DFonMor/Goniometro-Digital/Modelos 3D/goniometro.SLDASM

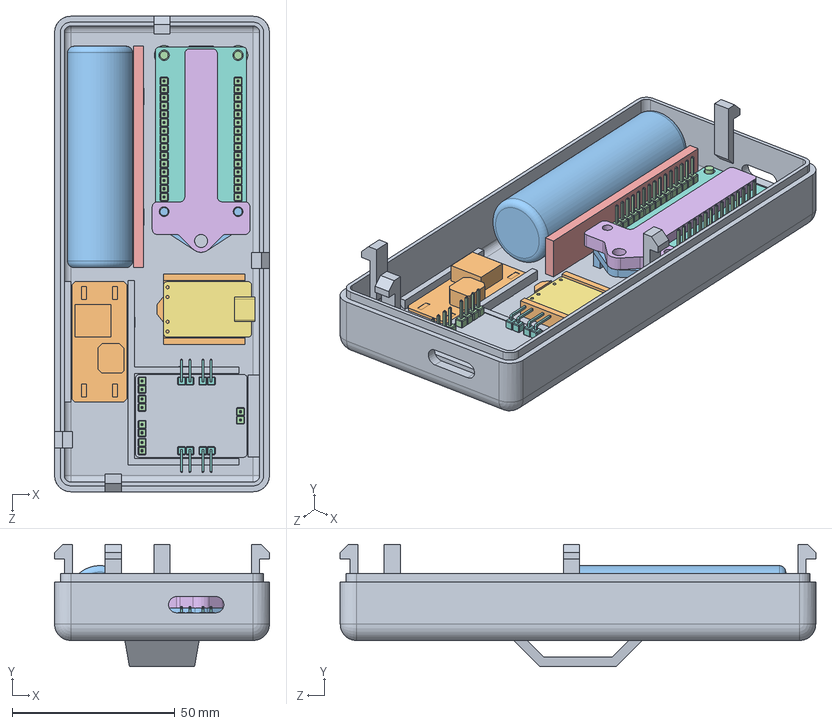
[picture p6: CAD file, 2026-04-27]
Modelos 3D/goniometro.SLDASM
66.0 x 37.5 x 146.0 mm
case_inferior
ESP32_board
esp32_connector x 2
ESP32_processor_base
ESP32_processor
pino x 40
bateria
modulo_step_up
pcb_sensor
pino_90 x 8
pcb_modulo_carregamento
suporte_esp
parede_bateria_esp32
pino_suporte x 2
sup_diant_esp32
sup_mod_carregamento
sup_latearal_pcb_sensor
