DFonMor/Goniometro-Digital/Modelos 3D/conj_pinos.SLDASM

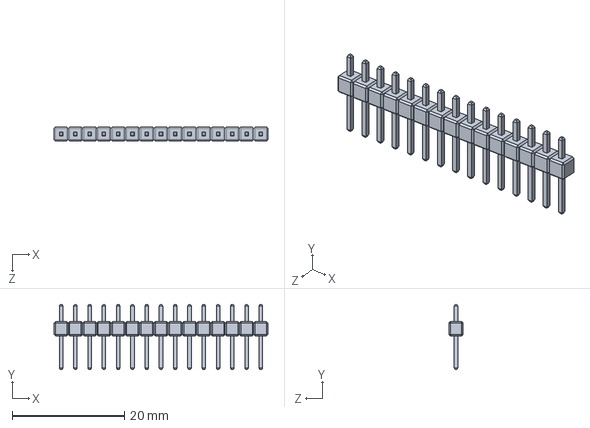
[picture p7: CAD file, 2026-04-27]
Modelos 3D/conj_pinos.SLDASM
38.1 x 11.6 x 2.54 mm
pino x 15
