DFonMor/Goniometro-Digital/Modelos 3D/case.SLDASM

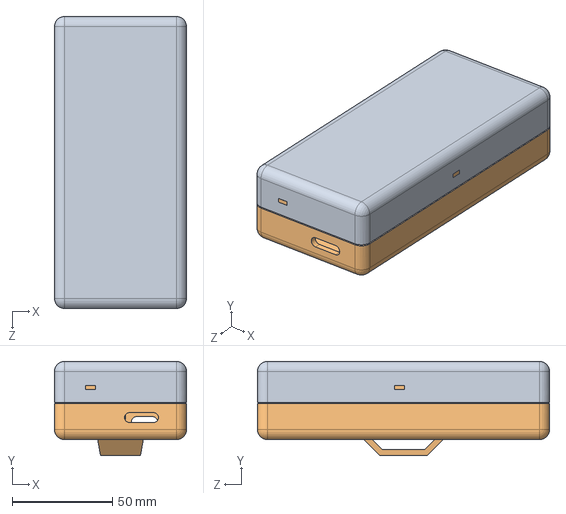
[picture p8: CAD file, 2026-04-27]
Modelos 3D/case.SLDASM
66.0 x 47.1 x 146.0 mm
case_inferior
case_superior
