DFonMor/Goniometro-Digital/Modelos 3D/modulo_carregamento.SLDASM

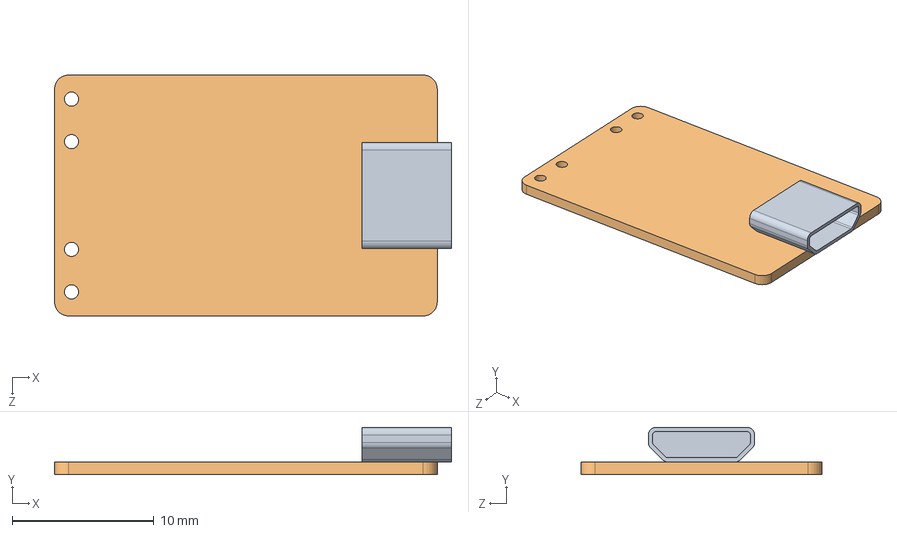
[picture p9: CAD file, 2026-04-27]
Modelos 3D/modulo_carregamento.SLDASM
28.0 x 3.35 x 17.0 mm
pcb_modulo_carregamento
esp32_connector
