DFonMor/Goniometro-Digital/Modelos 3D/pino_90.SLDPRT

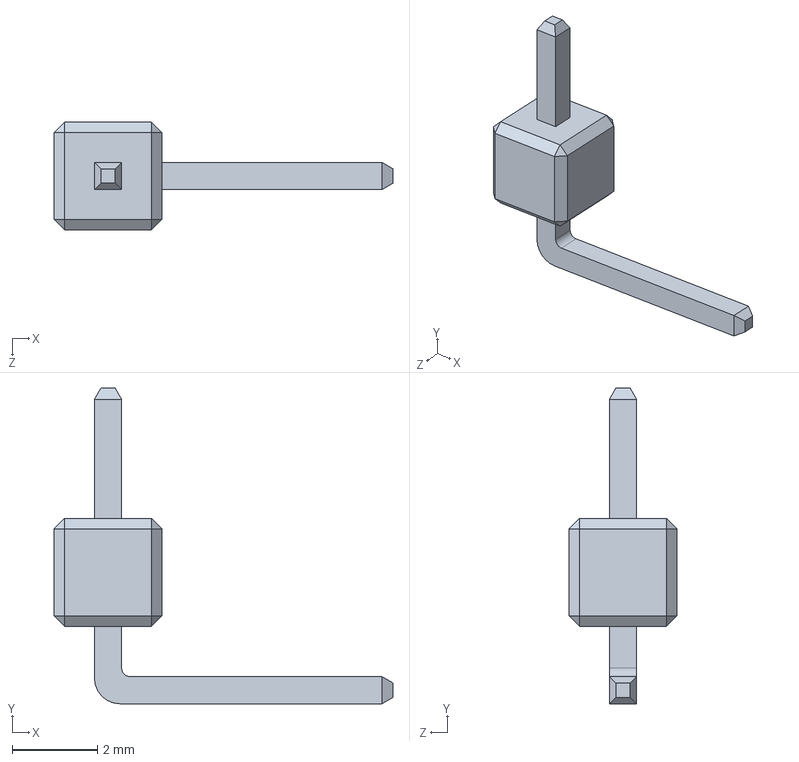
[picture p20: CAD file, 2026-04-27]
Modelos 3D/pino_90.SLDPRT
7.97 x 7.42 x 2.54 mm
