DFonMor/Goniometro-Digital/Modelos 3D/sup_diant_esp32.SLDPRT

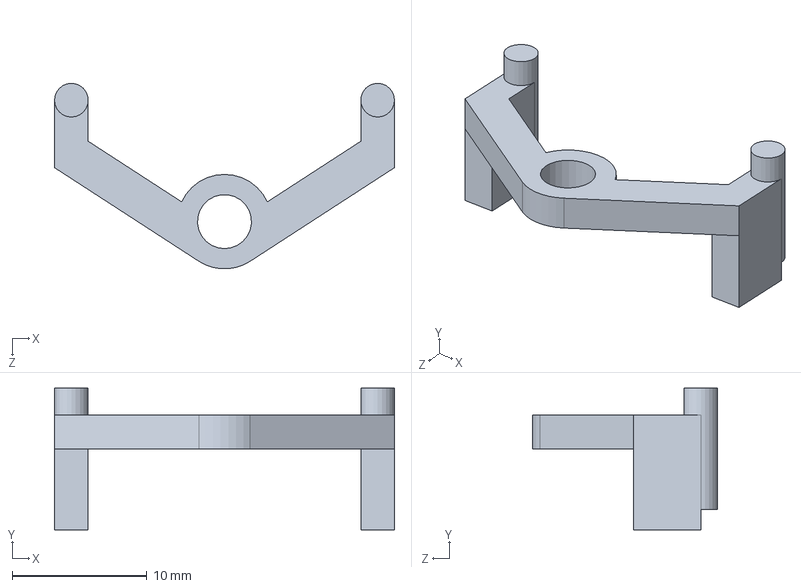
[picture p21: CAD file, 2026-04-27]
Modelos 3D/sup_diant_esp32.SLDPRT
25.2 x 10.5 x 13.7 mm
