DFonMor/Goniometro-Digital/Modelos 3D/case_inferior.SLDPRT

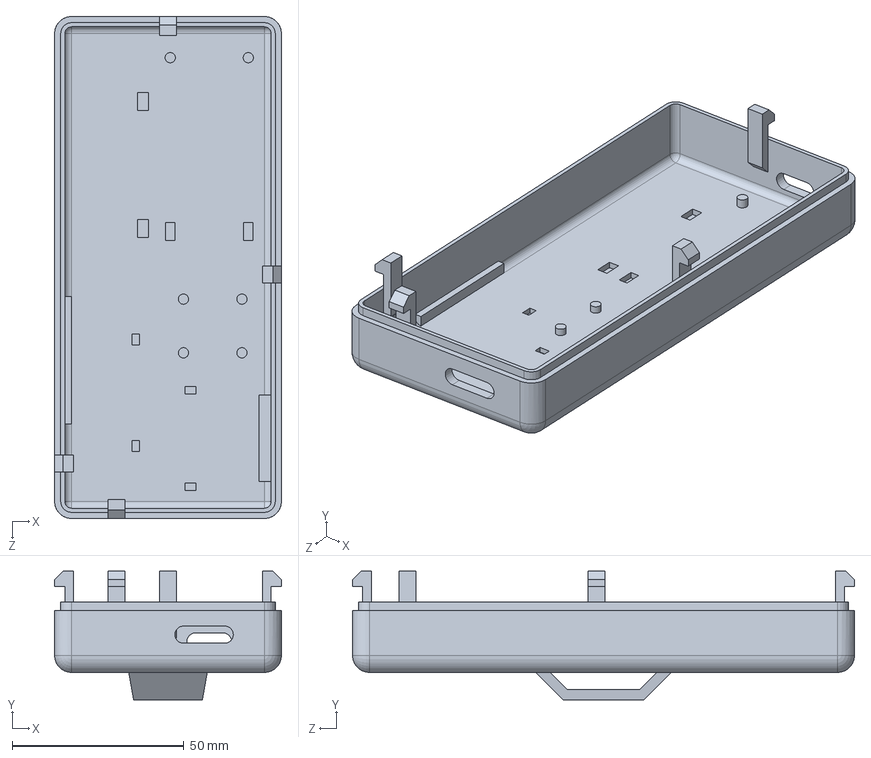
[picture p22: CAD file, 2026-04-27]
Modelos 3D/case_inferior.SLDPRT
66.0 x 37.5 x 146.0 mm
