DFonMor/Goniometro-Digital/Modelos 3D/case_superior.SLDPRT

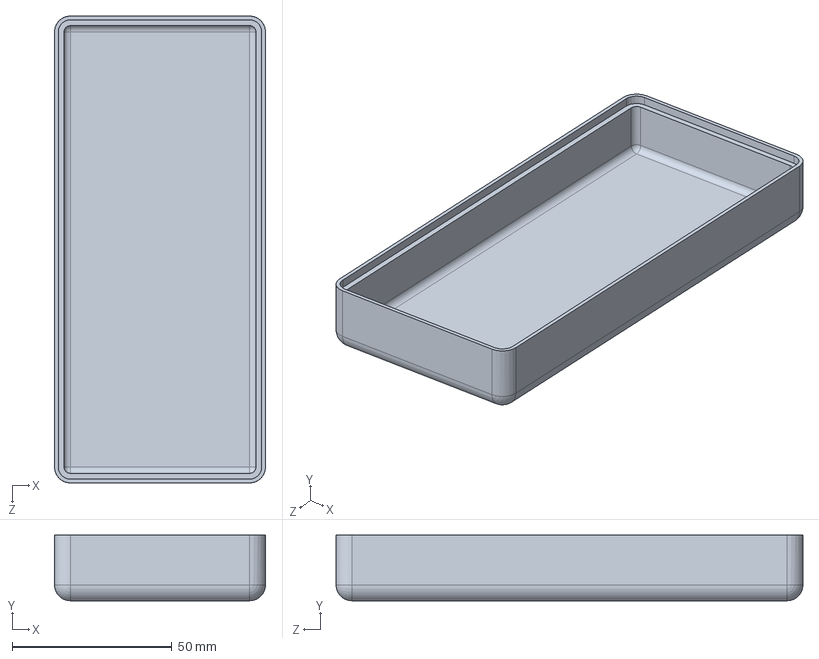
[picture p23: CAD file, 2026-04-27]
Modelos 3D/case_superior.SLDPRT
66.0 x 20.5 x 146.0 mm
