DFonMor/Goniometro-Digital/Modelos 3D/suporte_esp.SLDPRT

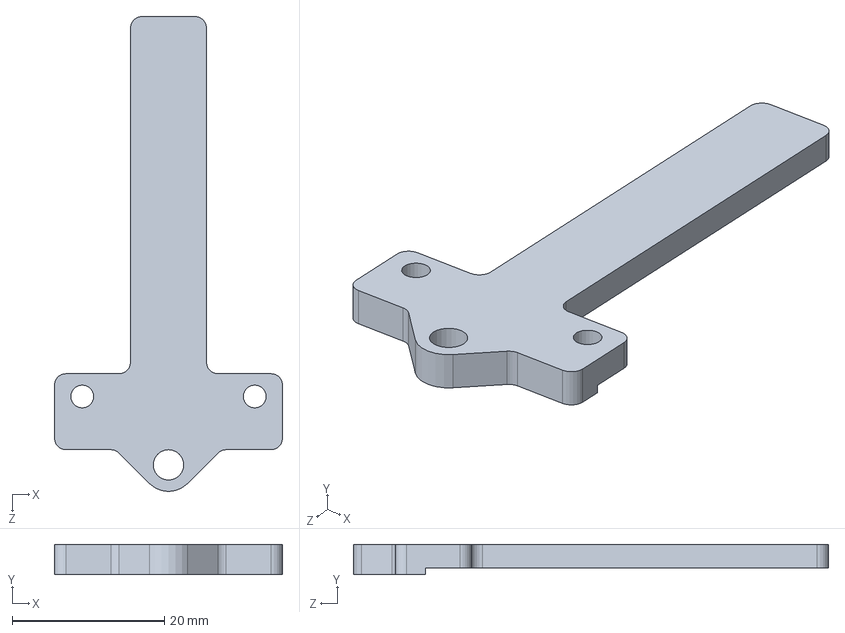
[picture p24: CAD file, 2026-04-27]
Modelos 3D/suporte_esp.SLDPRT
30.0 x 4.00 x 62.5 mm
