DFonMor/Goniometro-Digital/Modelos 3D/pcb_modulo_carregamento.SLDPRT

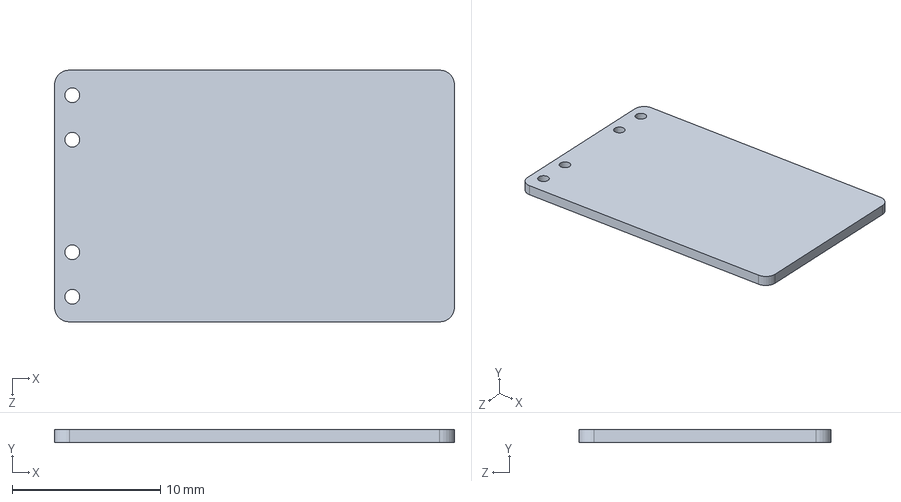
[picture p25: CAD file, 2026-04-27]
Modelos 3D/pcb_modulo_carregamento.SLDPRT
27.0 x 0.9 x 17.0 mm
