DFonMor/Goniometro-Digital/Modelos 3D/ESP32_processor_base.SLDPRT

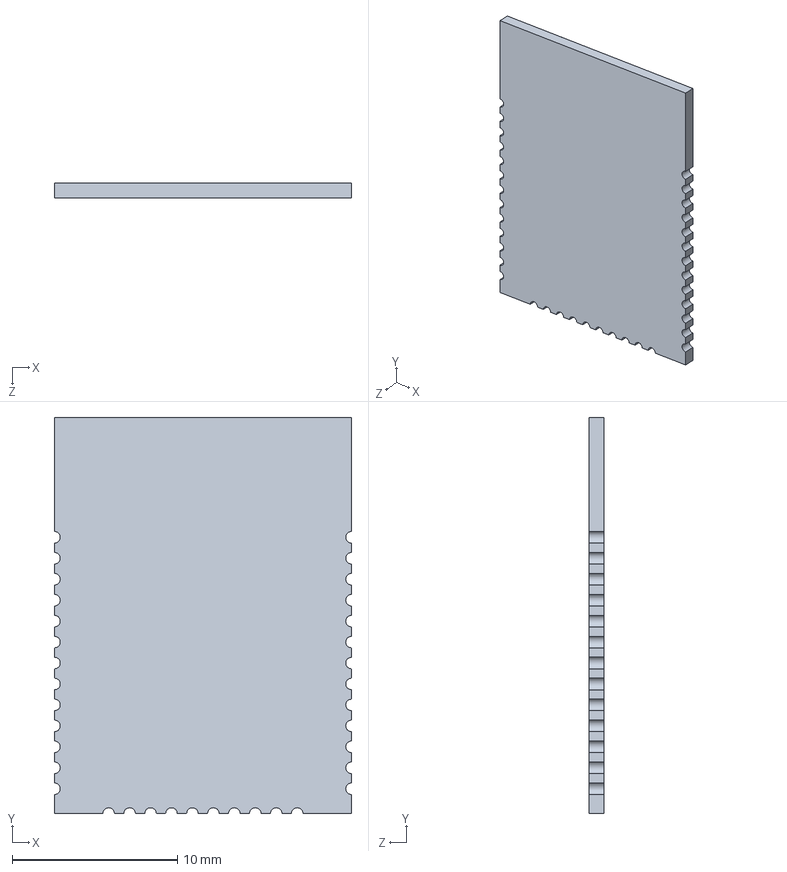
[picture p26: CAD file, 2026-04-27]
Modelos 3D/ESP32_processor_base.SLDPRT
18.0 x 24.0 x 0.9 mm
