DFonMor/Goniometro-Digital/Modelos 3D/pcb_sensor.SLDPRT

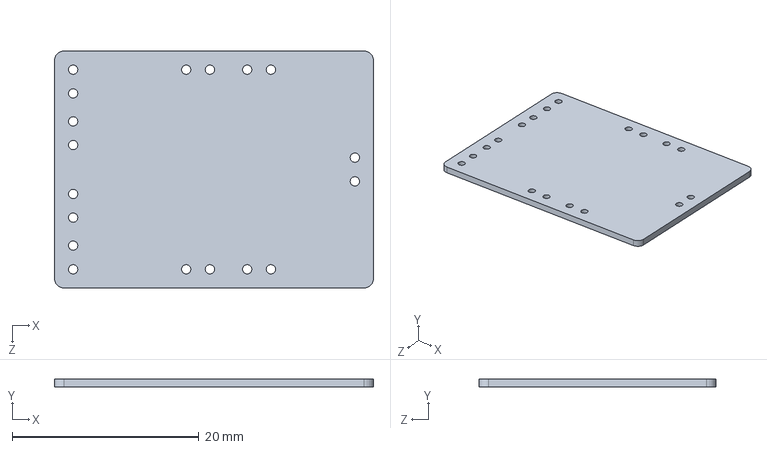
[picture p27: CAD file, 2026-04-27]
Modelos 3D/pcb_sensor.SLDPRT
34.2 x 0.9 x 25.4 mm
