DFonMor/Goniometro-Digital/Modelos 3D/pino.SLDPRT

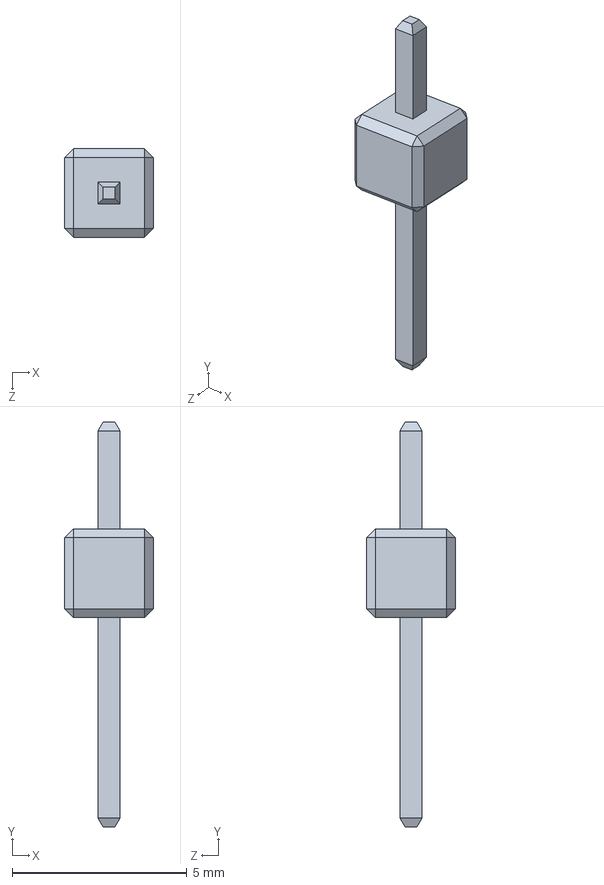
[picture p28: CAD file, 2026-04-27]
Modelos 3D/pino.SLDPRT
2.54 x 11.6 x 2.54 mm
